FakeNixie/Fake-Nixie/Dokumentazioa/Arduino/Azkenekoa/imagenFija.h

const unsigned short imagenFija[0x7E90] PROGMEM ={
  0x20C4,0x1862,0x3125,0x20A3,0x3986,0x20C4,0x2904,0x28C4,0x49C7,0x2082,0x3966,0x2904,0x3166,0x18A2,0x39A7,0x2904,0x3125,0x2904,0x3166,0x2924,0x2904,0x3124,0x3145,0x20E4,0x20C3,0x41C7,0x3166,0x3166,0x2925,0x39A7,0x20E4,0x39A6,0x28E4,0x41A7,0x28E4,0x41E7,0x18C3,0x2945,0x4A08,0x5AAA,0x18C4,0x41C8,0x3145,0x3966,0x3986,0x5248,0x2104,0x39A6,0x3186,0x3186,0x41E7,0x41E7,0x4208,0x39A6,0x39A7,0x2945,0x5229,0x39A7,0x4A27,0x20C2,0x5A89,0x41A7,0x6B2C,0x2104,0x526A,0x3186,0x4A6A,0x20E4,0x5AAB,0x39C7,0x39A7,0x2104,0x62EC,0x39A7,0x4A29,0x4208,0x4A69,0x3186,0x39C7,0x4208,0x39A6,0x41C7,0x39C6,0x41E7,0x39A6,0x41E7,0x3166,0x39C8,0x39C7,0x528A,0x18E3,0x4228,0x39E7,0x3186,0x39C6,0x41E7,0x5A89,0x3965,0x49E6,0x49E8,0x4A27,0x2104,0x39C7,0x5269,0x62EB,0x20C3,0x4A08,0x526A,0x4A29,0x39A7,0x3185,0x4A48,0x4A29,0x4208,0x20E4,0x526A,0x3186,0x3166,0x3166,0x52AB,0x2966,0x3186,0x2924,0x39C7,0x3165,0x2945,0x39A7,0x41C7,0x3166,0x2945,0x2945,0x4208,0x39A7,0x3166,0x28E4,
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

};
