FakeNixie/Fake-Nixie/Dokumentazioa/Arduino/Azkenekoa/nixieClockConfig.h

//Define your SSID and Password here
#define SECRET_SSID ""
#define SECRET_PASS ""

//Define the Daylight Saving rule here
#define DST_RULE ""
//the rules are available here https://github.com/nayarsystems/posix_tz_db/blob/master/zones.csv
